mokeylaser/MokeyLaserV1/MokeyLaserV1_Images/20220820_162253.jpg

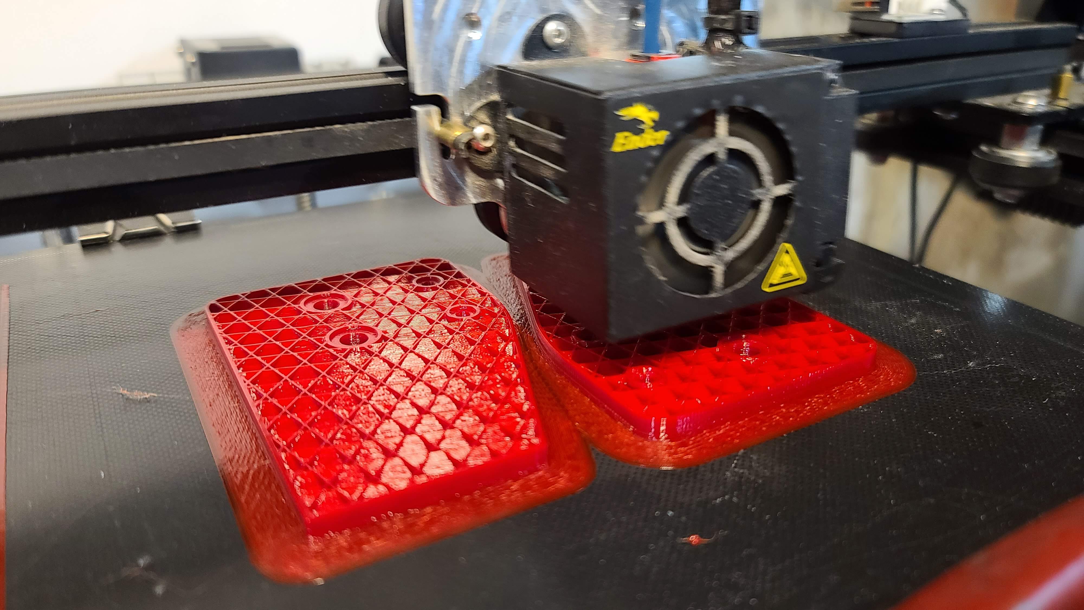
MokeyLaserV1_Images/20220820_162253.jpg
