mokeylaser/MokeyLaserV1/MokeyLaserV1_Images/20220824_193659.jpg

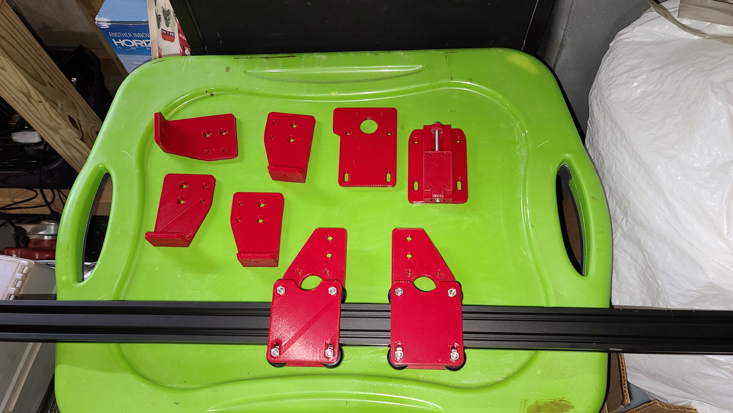
MokeyLaserV1_Images/20220824_193659.jpg
