mokeylaser/MokeyLaserV1/MokeyLaserV1_Images/20220825_105800.jpg

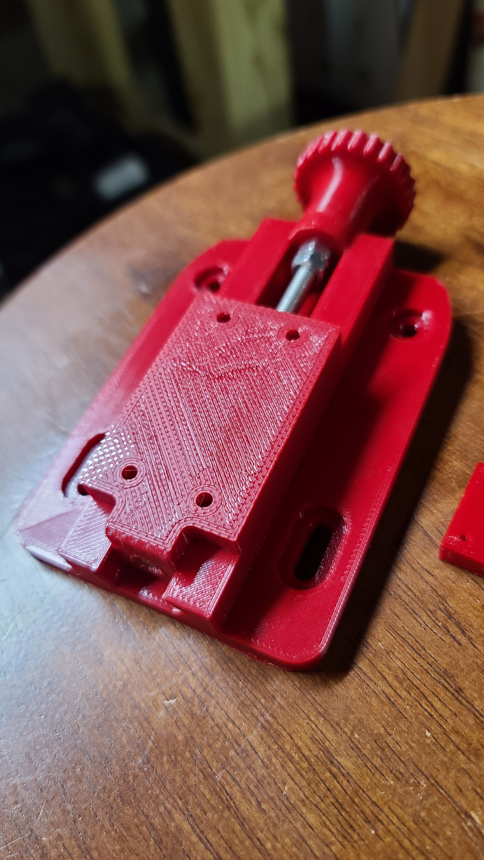
MokeyLaserV1_Images/20220825_105800.jpg
