mokeylaser/MokeyLaserV1/MokeyLaserV1_Images/20220827_165122.jpg

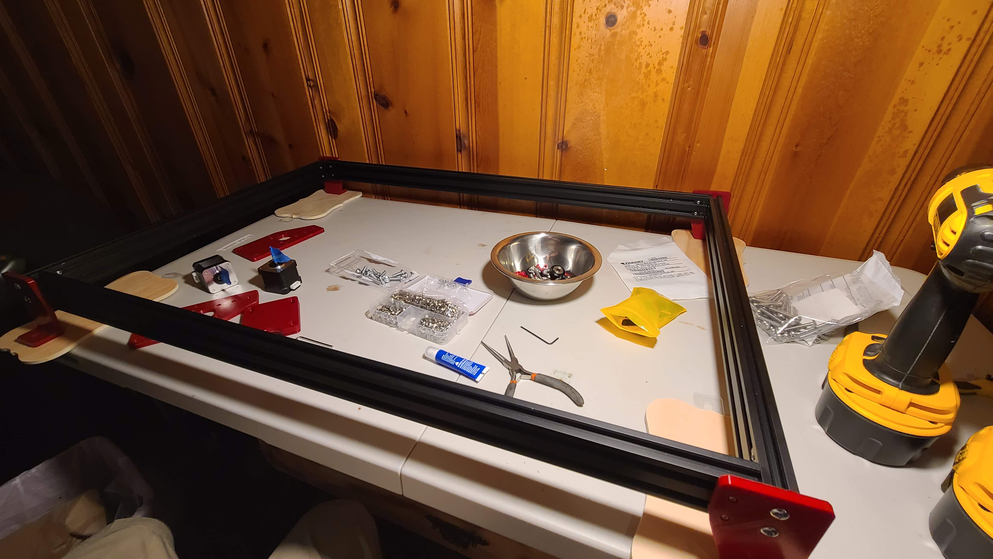
MokeyLaserV1_Images/20220827_165122.jpg
