mokeylaser/MokeyLaserV1/MokeyLaserV1_Images/20220827_171425.jpg

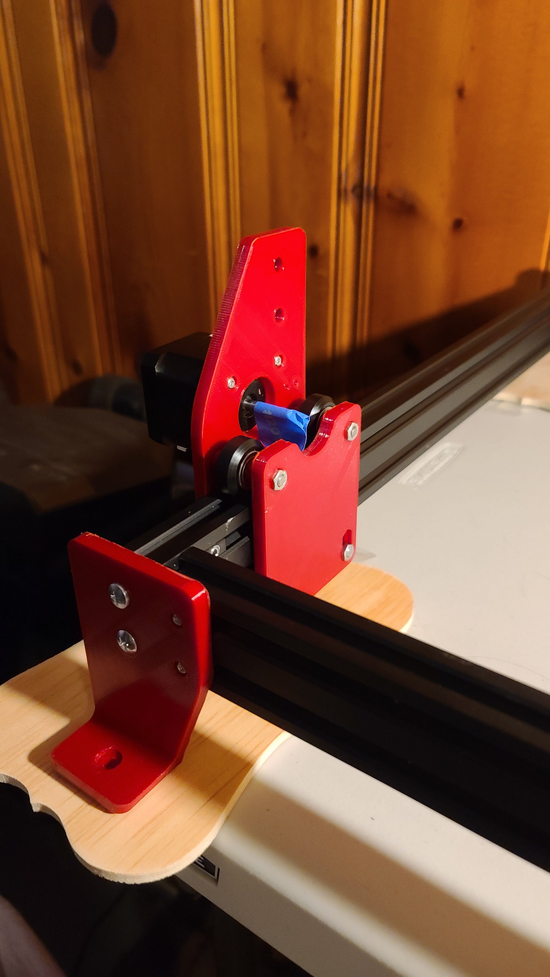
MokeyLaserV1_Images/20220827_171425.jpg
