mokeylaser/MokeyLaserV1/MokeyLaserV1_Images/20220827_191200.jpg

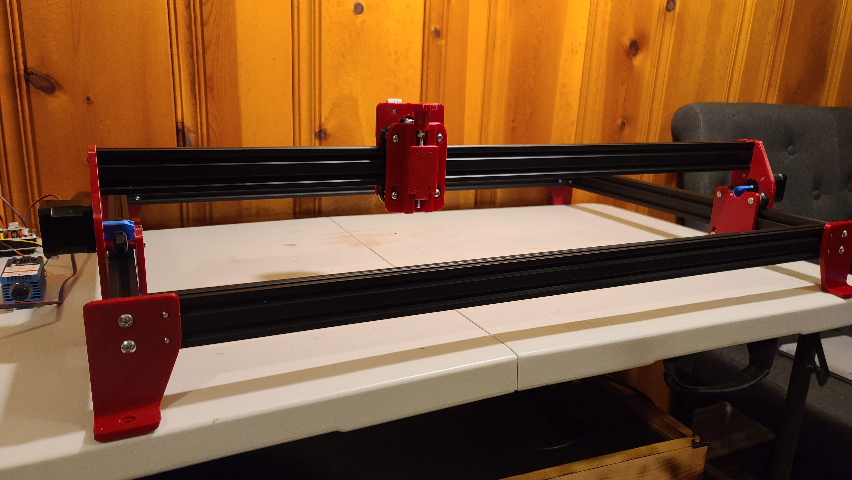
MokeyLaserV1_Images/20220827_191200.jpg
