mokeylaser/MokeyLaserV1/CAD_Models_V1/02 Laser holder base v1.step

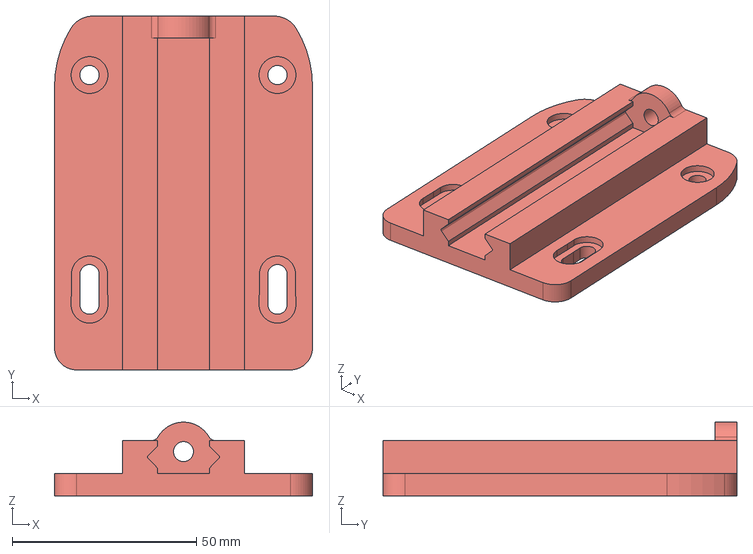
[picture p26: CAD file, 2022-09-06]
CAD_Models_V1/02 Laser holder base v1.step
70.0 x 96.0 x 20.0 mm
