mokeylaser/MokeyLaserV1/MokeyLaser_v1.1/E-Stop box top.stl

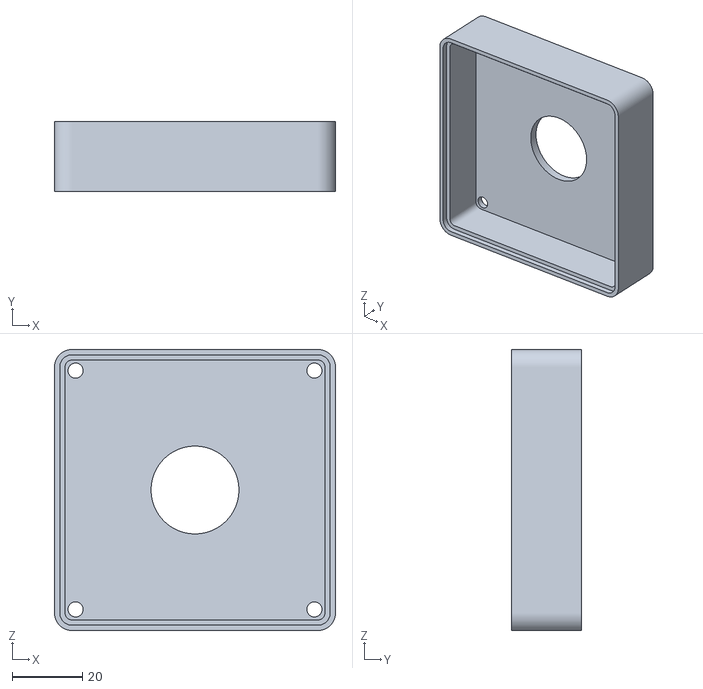
[picture p27: CAD file, 2023-01-19]
MokeyLaser_v1.1/E-Stop box top.stl
80.0 x 20.0 x 80.0
