mokeylaser/MokeyLaserV1/MokeyLaserV1_STLs/Uno and CNC Shield holder v2.stl

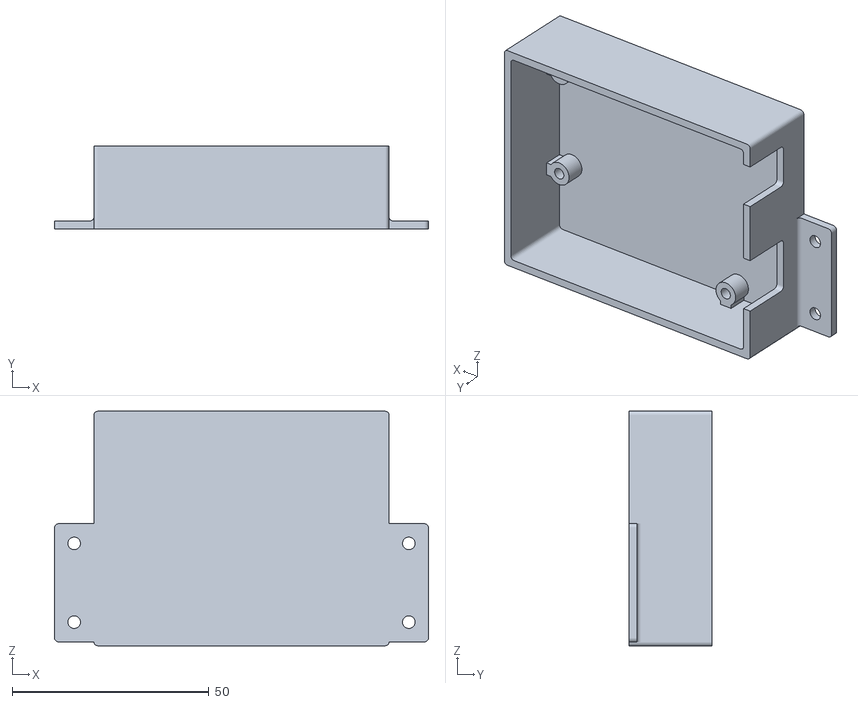
[picture p28: CAD file, 2022-09-06]
MokeyLaserV1_STLs/Uno and CNC Shield holder v2.stl
95.0 x 21.0 x 59.6
