mokeylaser/MokeyLaserV1/MokeyLaser_v1.1/MKS-DLC32_Enclosure_BodyV1.stl

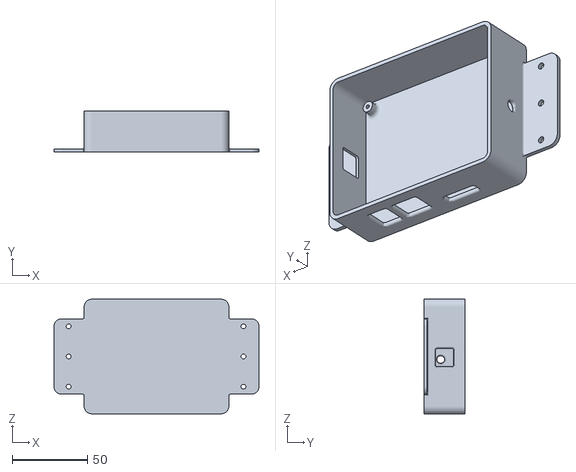
[picture p29: CAD file, 2023-01-19]
MokeyLaser_v1.1/MKS-DLC32_Enclosure_BodyV1.stl
136.0 x 27.0 x 76.0
