mokeylaser/MokeyLaserV1/MokeyLaser_v1.1/05 V-Wheel Bushing v1.stl

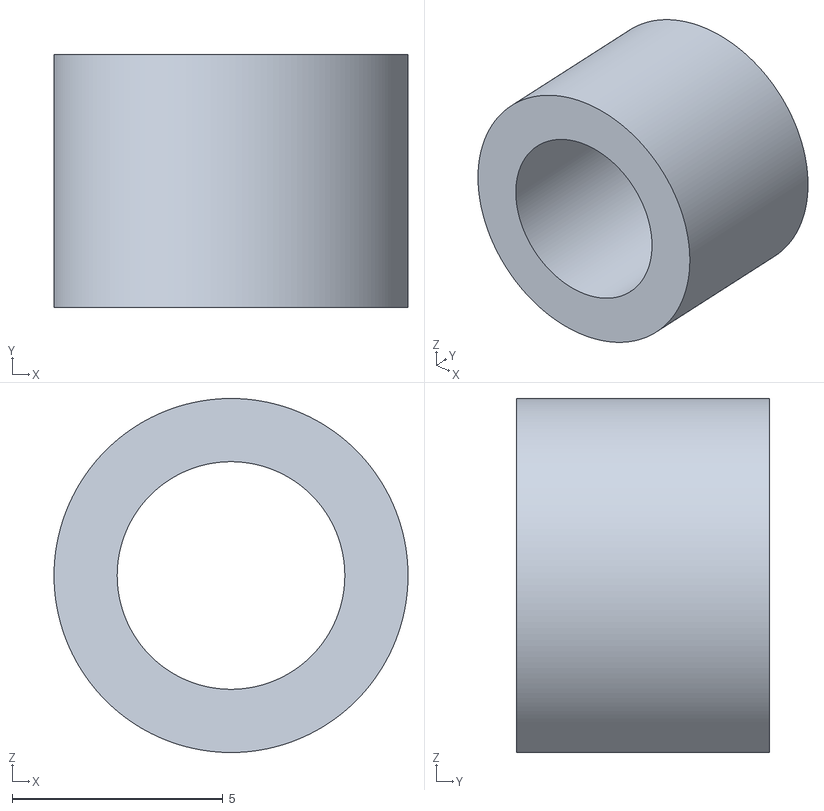
[picture p30: CAD file, 2023-01-19]
MokeyLaser_v1.1/05 V-Wheel Bushing v1.stl
8.40 x 6.00 x 8.40
