mokeylaser/MokeyLaserV1/MokeyLaser_v1.1/do_not_print_2040 V-Slot 796mm v3.stl

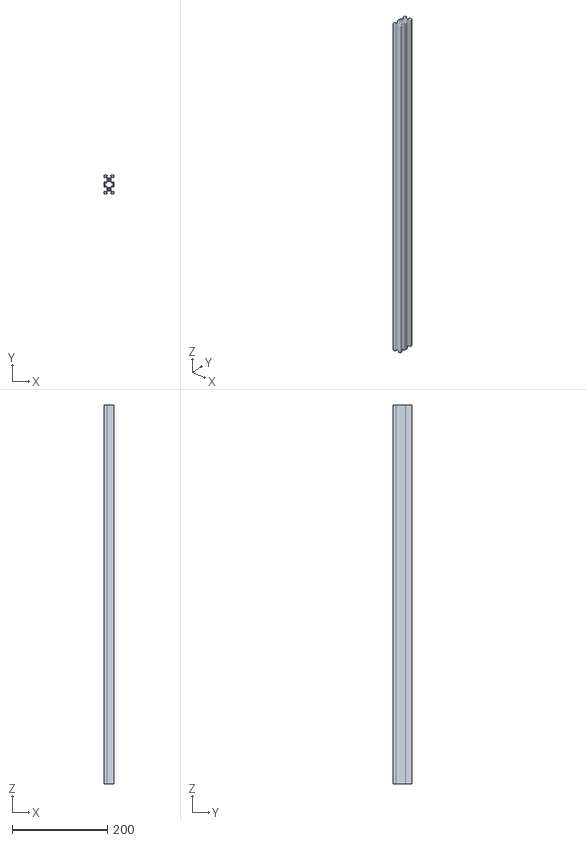
[picture p31: CAD file, 2023-01-19]
MokeyLaser_v1.1/do_not_print_2040 V-Slot 796mm v3.stl
20.0 x 40.0 x 796.0
