mokeylaser/MokeyLaserV1/MokeyLaser_v1.1/E-Stop box bottom.stl

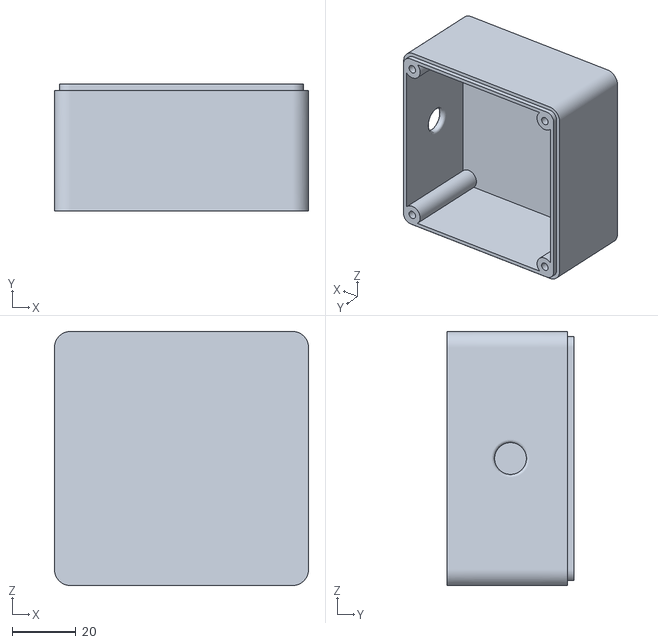
[picture p32: CAD file, 2023-01-19]
MokeyLaser_v1.1/E-Stop box bottom.stl
80.0 x 40.0 x 80.0
