mokeylaser/MokeyLaserV1/MokeyLaser_v1.1/do_not_print_Emergency Stop Switch v1 v1.stl

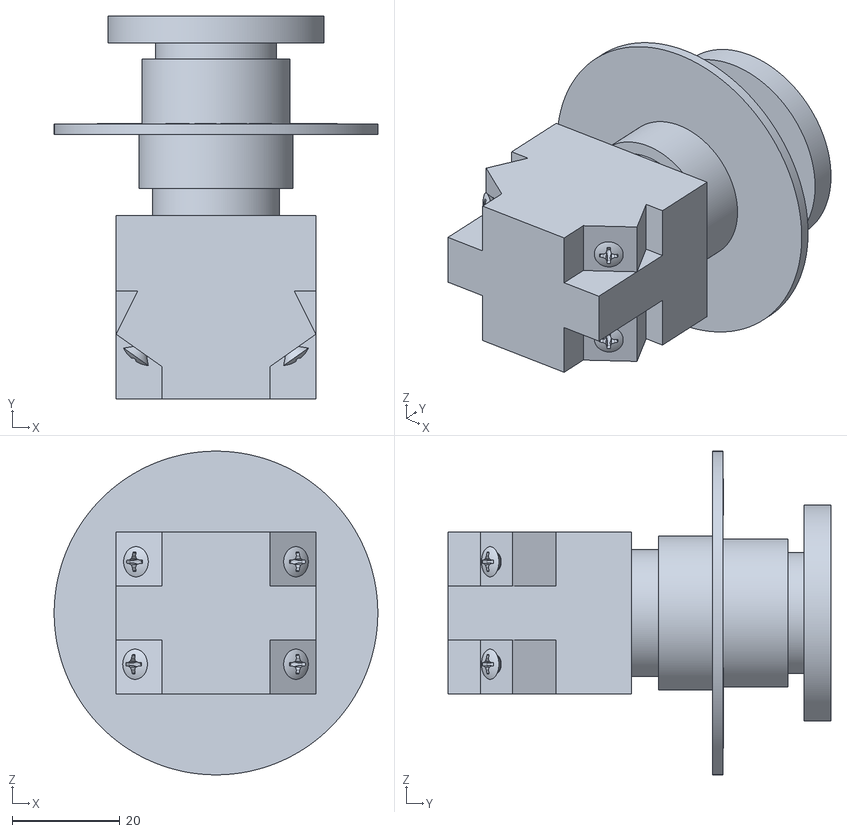
[picture p33: CAD file, 2023-01-19]
MokeyLaser_v1.1/do_not_print_Emergency Stop Switch v1 v1.stl
60.0 x 71.0 x 60.0
