mokeylaser/MokeyLaserV1/MokeyLaser_v1.1/do_not_print_LASER 5500mW v2.stl

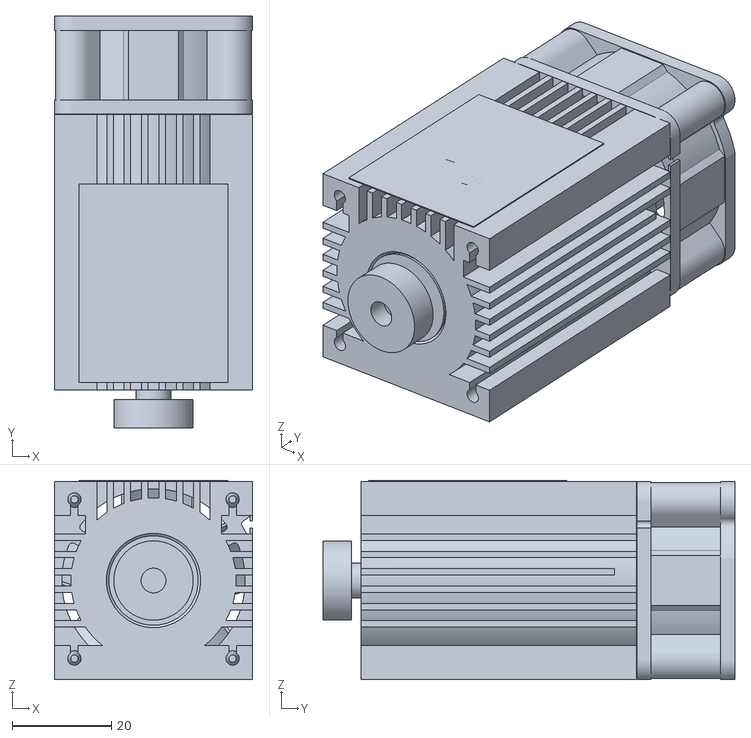
[picture p34: CAD file, 2023-01-19]
MokeyLaser_v1.1/do_not_print_LASER 5500mW v2.stl
40.0 x 83.1 x 40.2
