mokeylaser/MokeyLaserV1/MokeyLaser_v1.1/01 Laser Mount 16mm x 40mm M3 LA-2 v3.stl

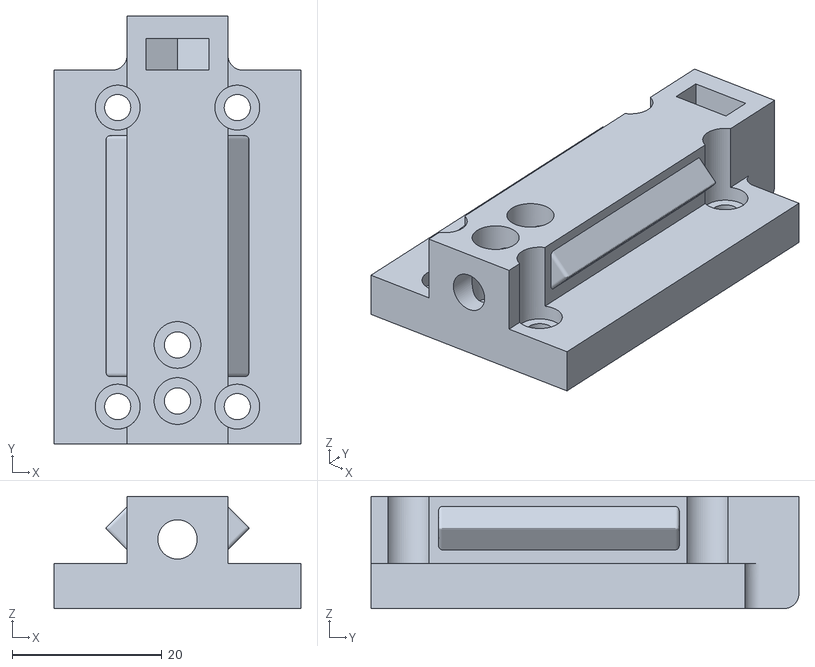
[picture p35: CAD file, 2023-01-19]
MokeyLaser_v1.1/01 Laser Mount 16mm x 40mm M3 LA-2 v3.stl
33.0 x 57.2 x 15.0
